Meebleeps/MeeBleeps-Mutant-Synth/src/avSequencer.h

/*----------------------------------------------------------------------------------------------------------
 * avSequencer.h
 * 
 * Defines a generative sequencer with multiple generative algorithms, musical scale quantisation,
 * variable sequence length (up to 16 steps) and multiple parameter-lock (motion-sequencing) channels
 * 
 * (C) 2021 Meebleeps
*-----------------------------------------------------------------------------------------------------------
*/

#ifndef avSequencer_h
#define avSequencer_h

#include "Arduino.h"
#include <EventDelay.h>
#include <ADSR.h>


#define MAX_SEQUENCE_LENGTH 16
#define MAX_SCALE_LENGTH 12

#define SCALEMODE_MAJOR 0
#define SCALEMODE_MINOR 1
#define SCALEMODE_PENTA 2
#define SCALEMODE_GOA 3
#define SCALEMODE_OCTAVE 4
#define SCALEMODE_FIFTHS 5
#define MAX_SCALE_COUNT 6

#define MUTATE_ALGO_DEFAULT     0
#define MUTATE_ALGO_ARPEGGIATED 1
#define MAX_MUTATE_ALGO_COUNT   2

#define MUTATE_MAX_OCTAVE_SPREAD 3

#define AUDIO_OUTPUT_LATENCY_COMPENSATION_MICROS 8000
#define SYNC_STEPS_PER_PULSE 2
#define SYNC_STEPS_PER_TAP 4
#define MAX_PARAMETER_LOCKS 6


//#define SEQUENCER_TESTMODE

class MutatingSequencer
{
  public:
    MutatingSequencer();
    MutatingSequencer(byte stepCount, byte scaleCount);

    void start();
    void stop();
    void toggleStart();
    
    void newSequence(byte seqLength);
    void testSequence();
    
    void mutateSequence();
    void mutateSequenceDefault();
    void mutateSequenceArp();
    void mutateNoteLength();
    void mutateMutation();
    
    void nextStep(bool restart);
    bool update(bool restart);      //returns true if sequencer moved to next step
    void syncPulse(int stepsPerClick);   //accepts a sync pulse to synchronise the timer
    int8_t outputSyncPulse(); 
    
    void print();
    void printParameters();
    void printSequence();

    void setScale(uint8_t  scaleMode);
    uint8_t getScale();

    void setTonic(int8_t newTonic);
    int8_t getTonic();
    
    void setRetrigger(bool newRetrigState);

    void setParameterLock(byte channel, int value);
    int  getParameterLock(byte channel);
    void clearAllParameterLocks(byte channel);
    
    void      setNextNoteLength(uint16_t newNoteLength);
    uint16_t  getNextNoteLength();

    void setScatterProbability(byte newScatter);
    byte getScatterProbability();
    bool isScattered();

    void setNoteProbability(byte newProbability);
    byte getNoteProbability();

    void setMutationProbability(byte newProbability);
    byte getMutationProbability();
    
    byte getCurrentNote();
    byte getCurrentStep();
    
    byte getSequenceLength();
    void setSequenceLength(byte newLength);

    byte getDuckingEnvelope();
    int  getDuckingAmount();
    void  setDuckingAmount(int newDuckingAmount);
    
    uint8_t getAlgorithm();
    void setAlgorithm(uint8_t newValue);
    void nextAlgorithm();
    
  protected:
    byte mutationProbability;
    byte noteProbability;
    byte tonicProbability;
    byte rachetProbability;     // not used in final design
    byte scatterProbability;    // not used in final design
    byte shufflePct;            // not used in final design
    byte mutationAlgorithm;

    byte sequenceLength;
    byte scaleNoteCount;
    uint16_t nextStepNoteLength;

    bool retrigState = false;
    byte retrigStep = 0;

    byte currentNote = 0;
    byte currentStep = 0;                    

    int parameterLocks[MAX_PARAMETER_LOCKS][MAX_SEQUENCE_LENGTH];

    //byte syncPulseSteps;
    byte syncPulseClockDivide;              //todo allow fractional to accelerate clock

    uint32_t timeSinceLastSyncPulseMicros;
    uint32_t lastSyncPulseTimeMicros;
    uint32_t lastStepTimeMicros;
    uint32_t nextStepTimeMicros;
    uint32_t nextStepTimeMillis;
    
    bool running;

    uint8_t currentScaleMode;
    byte tonicNote;                    

    byte bpm;
    byte notes[MAX_SEQUENCE_LENGTH];
    byte scaleNotes[MAX_SCALE_LENGTH];                  
    byte octaveSpread;

    ADSR <CONTROL_RATE, CONTROL_RATE> duckingEnvelope;
    int duckingAmount;
    
  private:
    bool _debugOutput;
    void initialiseScale(int scaleMode);
    EventDelay stepTimer;
    void setNextStepTimer();
    bool syncPulseLive;
    uint32_t syncPulseCount;

    byte duckingCounter;

    bool ignoreNextSyncPulse;
    
    
};

#endif
